macroxue/keyboard-diy/images/Right matrix.jpg

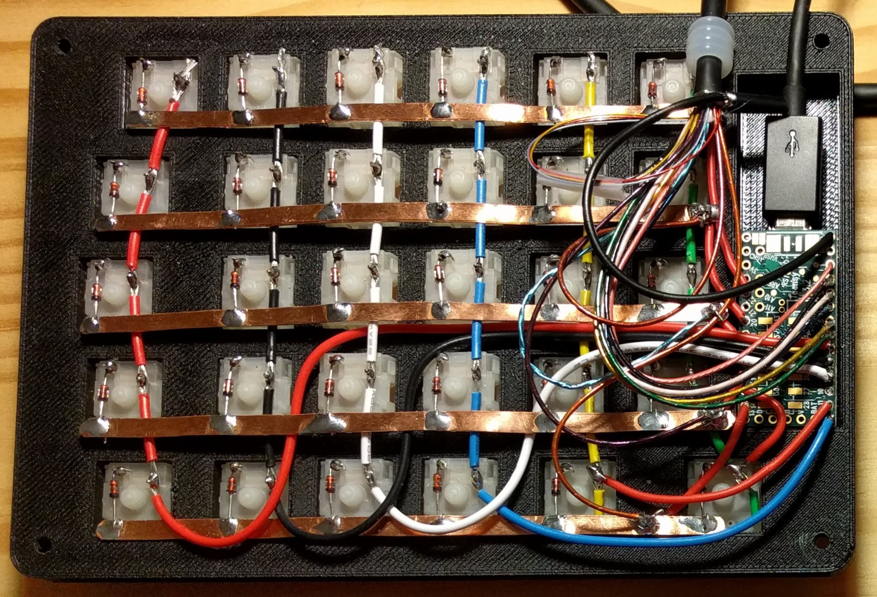
images/Right matrix.jpg
